mastmees/z-two/z80_tables.c

/* The MIT License (MIT)
 
  Copyright (c) 2018 Madis Kaal <mast@nomad.ee>
 
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
  THE SOFTWARE IS PROVIDED "AS IS", WITHOUT WARRANTY OF ANY KIND, EXPRESS OR
  IMPLIED, INCLUDING BUT NOT LIMITED TO THE WARRANTIES OF MERCHANTABILITY,
  FITNESS FOR A PARTICULAR PURPOSE AND NONINFRINGEMENT. IN NO EVENT SHALL THE
  AUTHORS OR COPYRIGHT HOLDERS BE LIABLE FOR ANY CLAIM, DAMAGES OR OTHER
  LIABILITY, WHETHER IN AN ACTION OF CONTRACT, TORT OR OTHERWISE, ARISING FROM,
  OUT OF OR IN CONNECTION WITH THE SOFTWARE OR THE USE OR OTHER DEALINGS IN THE
  SOFTWARE.
*/
#include "z80_flags.h"

const uint8_t z80_logicflags[256] = 
{
  0|ZFLAG|PVFLAG, //0
  0, //1
  0, //2
  0|PVFLAG, //3
  0, //4
  0|PVFLAG, //5
  0|PVFLAG, //6
  0, //7
  0, //8
  0|PVFLAG, //9
  0|PVFLAG, //10
  0, //11
  0|PVFLAG, //12
  0, //13
  0, //14
  0|PVFLAG, //15
  0, //16
  0|PVFLAG, //17
  0|PVFLAG, //18
  0, //19
  0|PVFLAG, //20
  0, //21
  0, //22
  0|PVFLAG, //23
  0|PVFLAG, //24
  0, //25
  0, //26
  0|PVFLAG, //27
  0, //28
  0|PVFLAG, //29
  0|PVFLAG, //30
  0, //31
  0, //32
  0|PVFLAG, //33
  0|PVFLAG, //34
  0, //35
  0|PVFLAG, //36
  0, //37
  0, //38
  0|PVFLAG, //39
  0|PVFLAG, //40
  0, //41
  0, //42
  0|PVFLAG, //43
  0, //44
  0|PVFLAG, //45
  0|PVFLAG, //46
  0, //47
  0|PVFLAG, //48
  0, //49
  0, //50
  0|PVFLAG, //51
  0, //52
  0|PVFLAG, //53
  0|PVFLAG, //54
  0, //55
  0, //56
  0|PVFLAG, //57
  0|PVFLAG, //58
  0, //59
  0|PVFLAG, //60
  0, //61
  0, //62
  0|PVFLAG, //63
  0, //64
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
  0|SFLAG, //242
  0|SFLAG|PVFLAG, //243
  0|SFLAG, //244
  0|SFLAG|PVFLAG, //245
  0|SFLAG|PVFLAG, //246
  0|SFLAG, //247
  0|SFLAG, //248
  0|SFLAG|PVFLAG, //249
  0|SFLAG|PVFLAG, //250
  0|SFLAG, //251
  0|SFLAG|PVFLAG, //252
  0|SFLAG, //253
  0|SFLAG, //254
  0|SFLAG|PVFLAG, //255
};
